pichenettes/shruthi-1/shruthi/hardware_design/documentation/response_notch_lp1.pdf

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

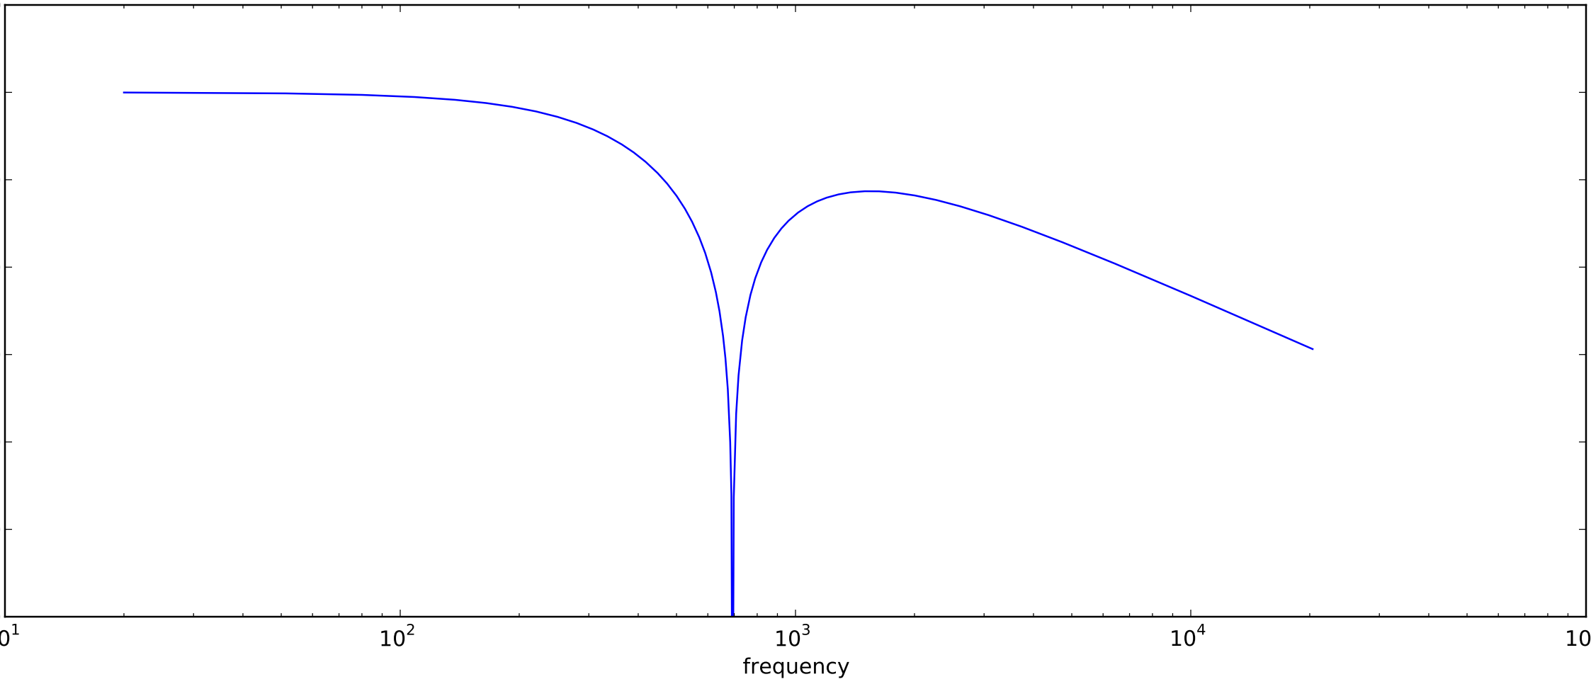
[picture p3: figure]
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
