pichenettes/shruthi-1/shruthi/hardware_design/documentation/response_phaser.pdf

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

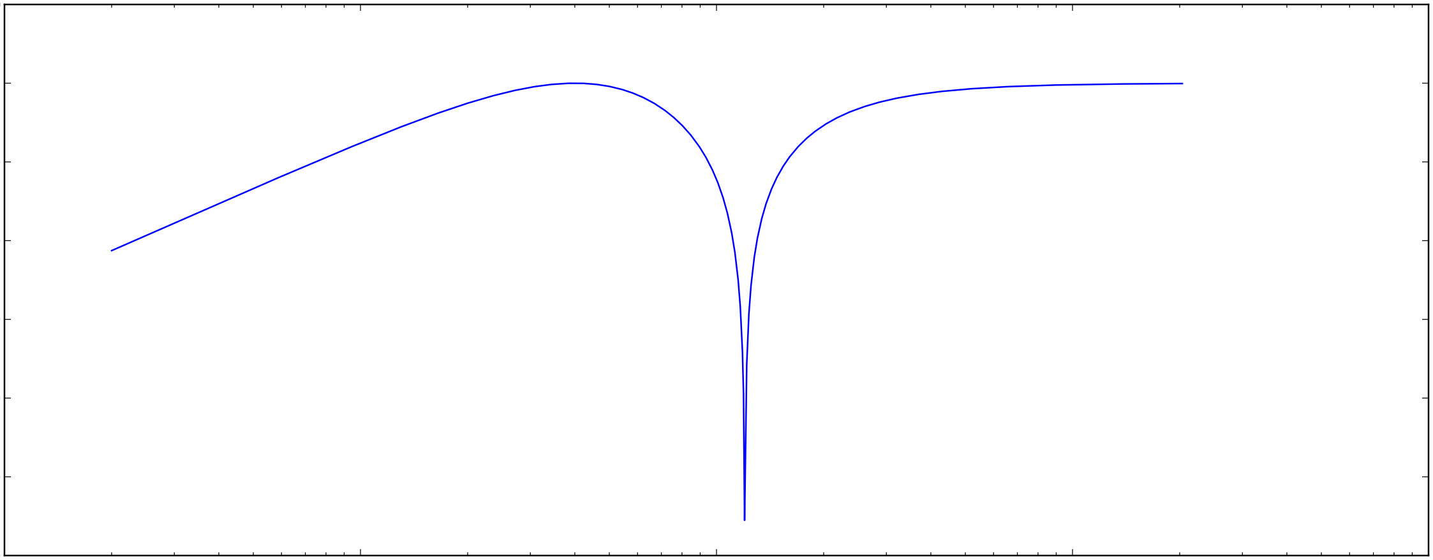
[picture p4: figure]
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
