pichenettes/shruthi-1/shruthi/hardware_design/documentation/smr4mkII_expo_current_source.pdf

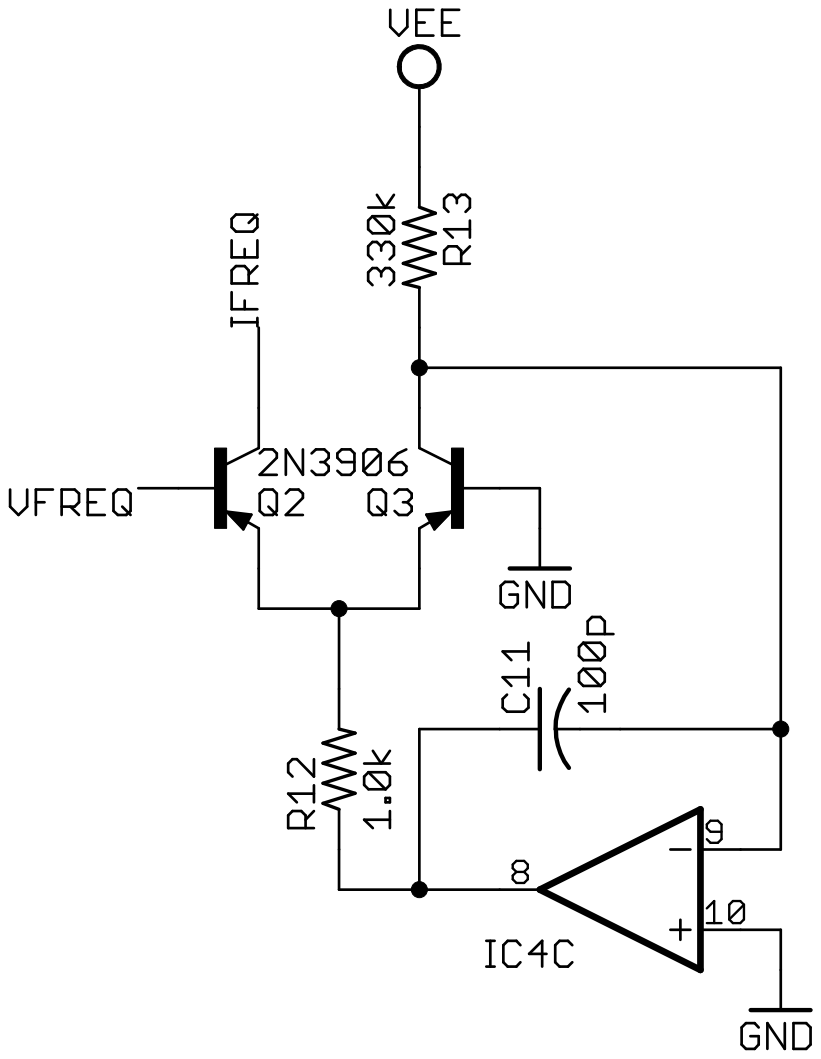
[picture p9: page 1]
