pichenettes/shruthi-1/shruthi/hardware_design/documentation/smr4mkII_linear_current_source.pdf

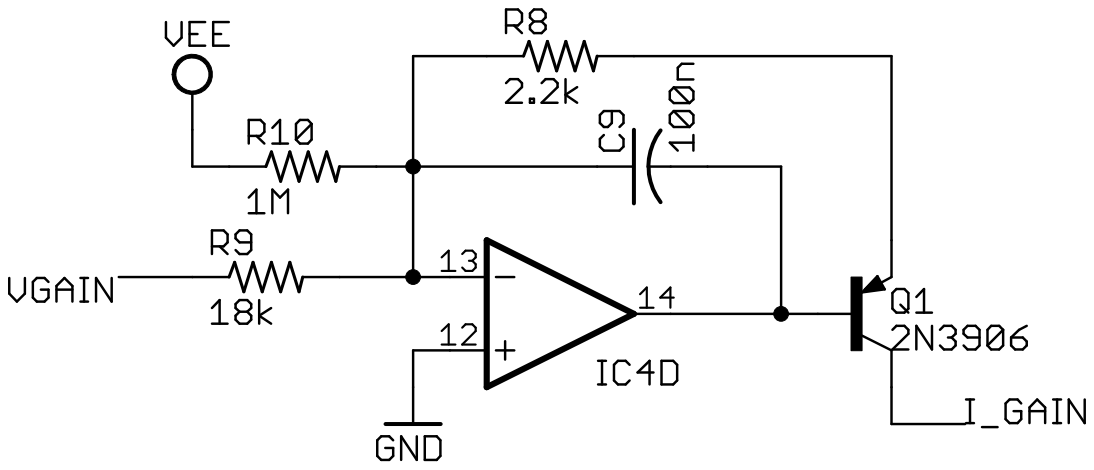
[picture p10: page 1]
