pichenettes/shruthi-1/shruthi/hardware_design/documentation/smr4mkII_otac_cell.pdf

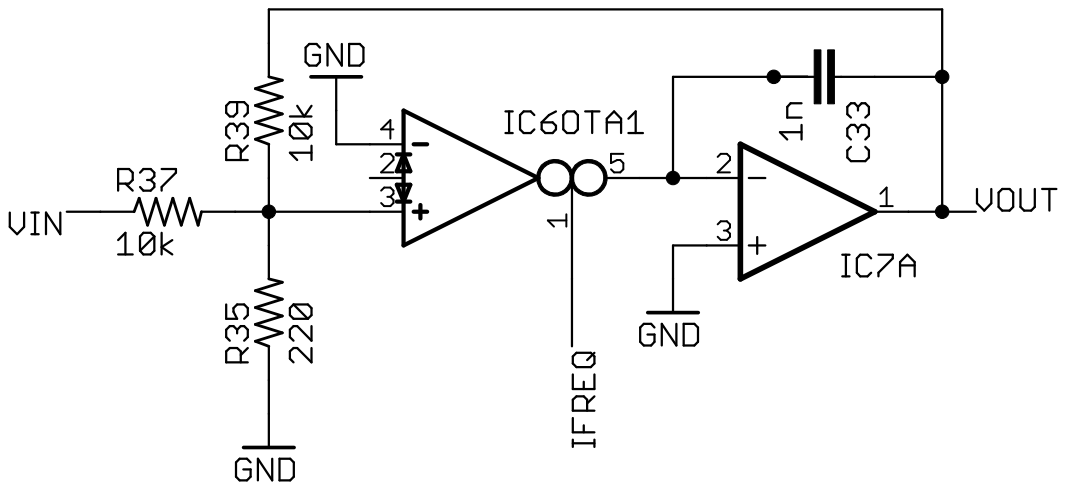
[picture p11: page 1]
