pichenettes/shruthi-1/shruthi/hardware_design/documentation/smr4mkII_scaling.pdf

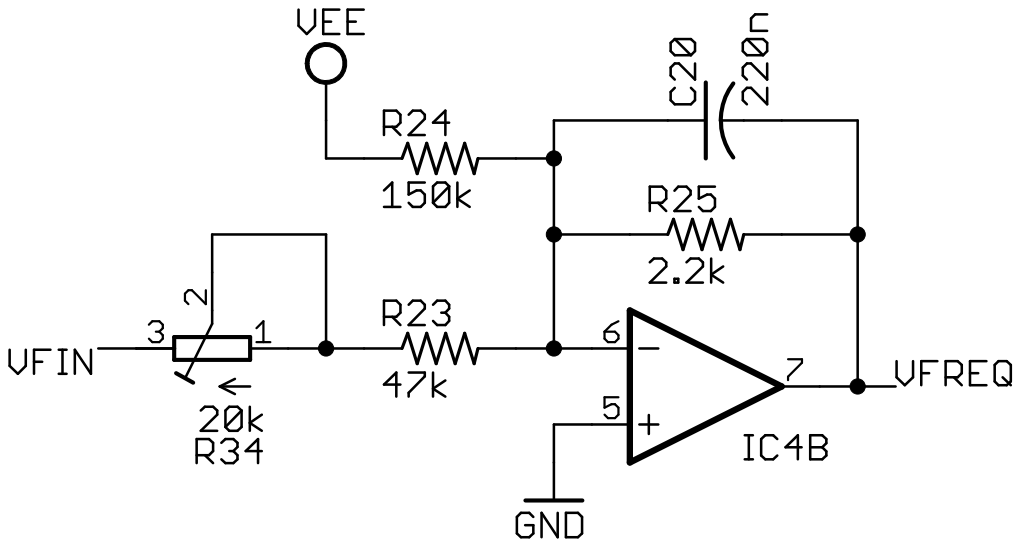
[picture p12: page 1]
