pichenettes/shruthi-1/shruthi/hardware_design/documentation/smr4mkII_vca.pdf

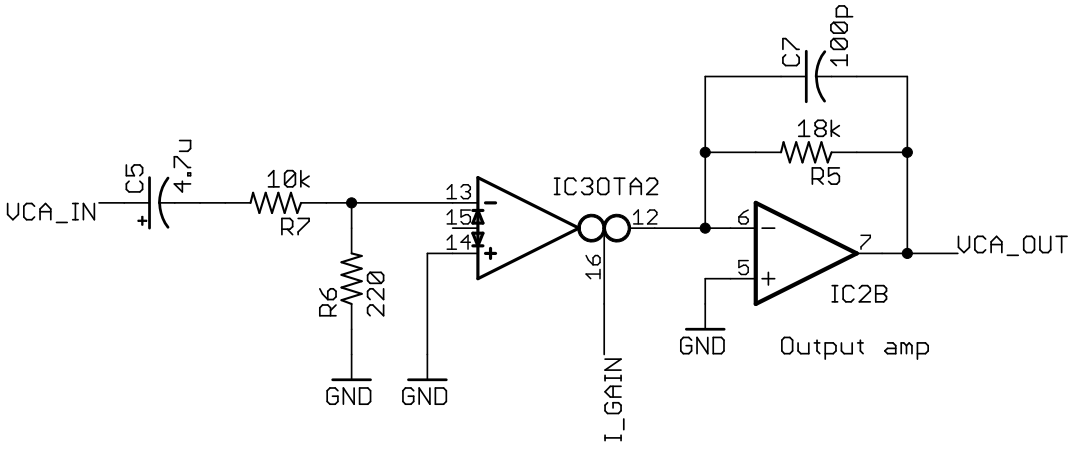
[picture p13: page 1]
