pichenettes/shruthi-1/shruthi/hardware_design/documentation/svf_schematics.pdf

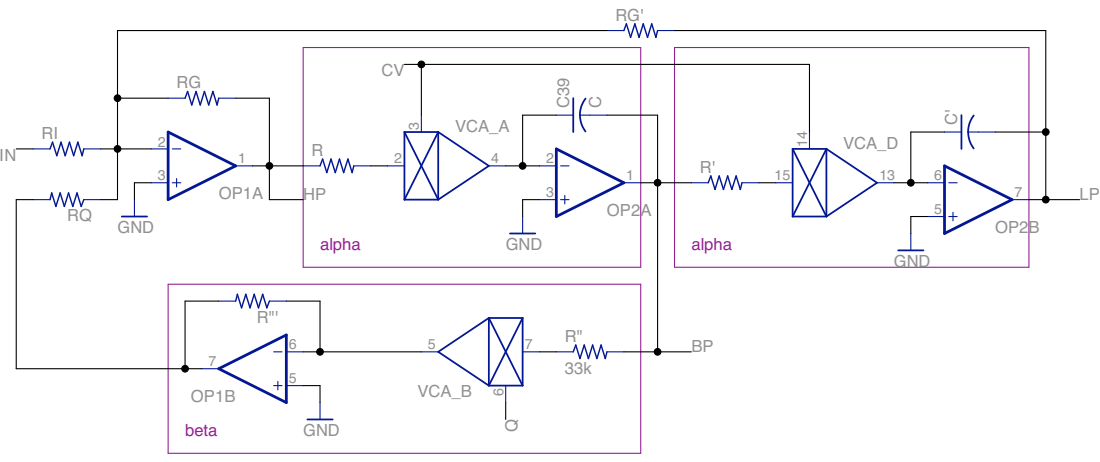
[picture p14: page 1]
