pichenettes/shruthi-1/shruthi/hardware_design/documentation/smr4_otac_cell.pdf

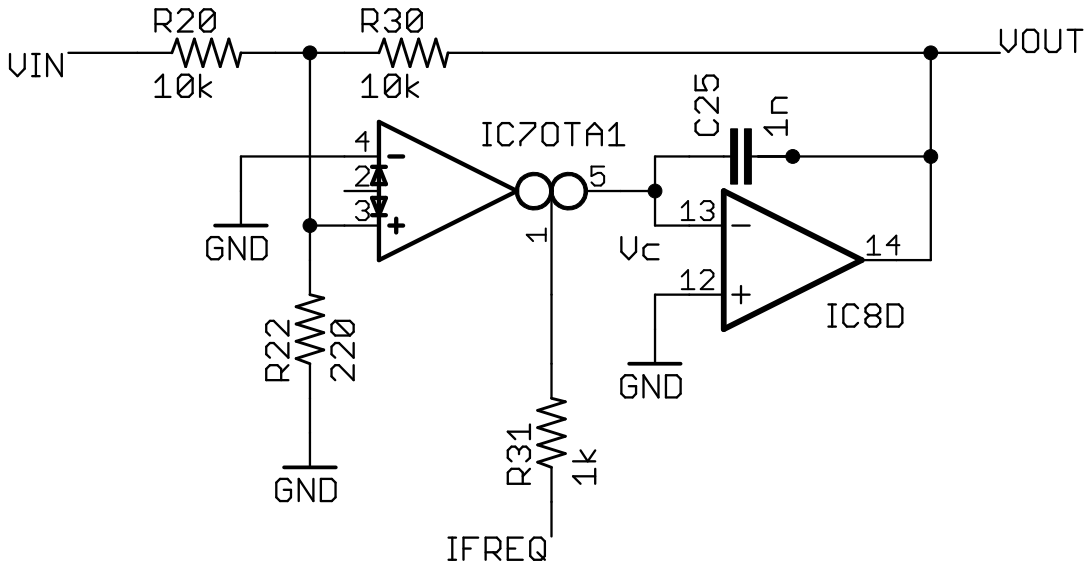
[picture p15: page 1]
