pichenettes/shruthi-1/shruthi/hardware_design/documentation/smr4_expo_current_source.pdf

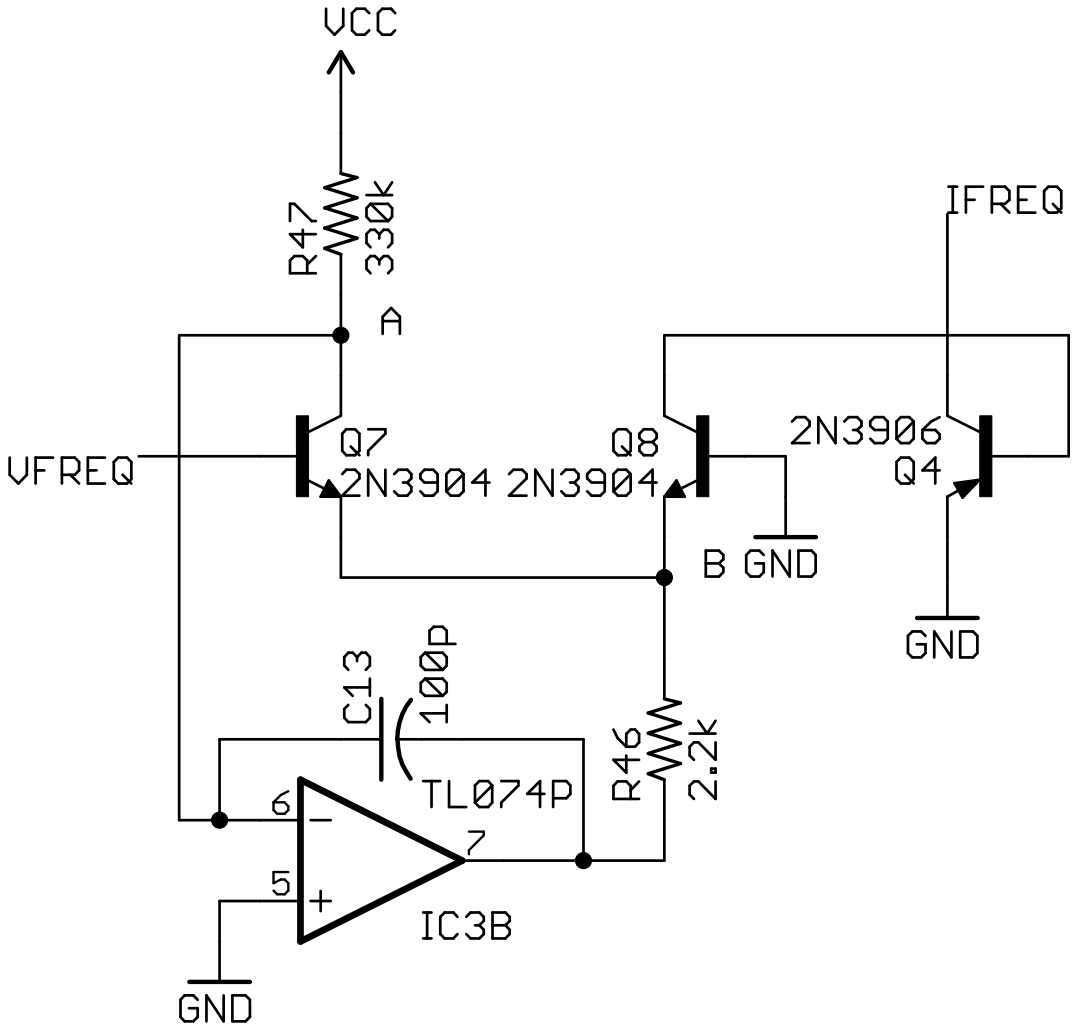
[picture p16: page 1]
