pichenettes/shruthi-1/shruthi/hardware_design/documentation/smr4_scaling.pdf

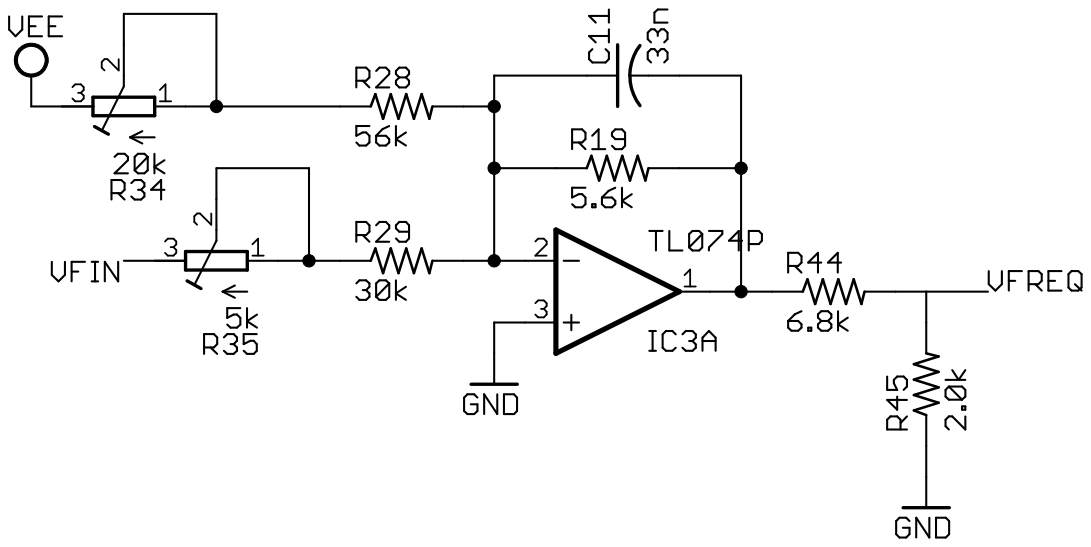
[picture p17: page 1]
