pichenettes/shruthi-1/shruthi/shruthi.h

// Copyright 2009 Emilie Gillet.
//
// Author: Emilie Gillet (emilie.o.gillet@gmail.com)
//
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
// -----------------------------------------------------------------------------
//
// Main definitions.

#ifndef SHRUTHI_SHRUTHI_H_
#define SHRUTHI_SHRUTHI_H_

#include "avrlib/base.h"

#include <avr/pgmspace.h>

namespace shruthi {

enum Switches {
  SWITCH_1,
  SWITCH_2,
  SWITCH_3,
  SWITCH_4,
  SWITCH_MODE,
  SWITCH_LOAD_SAVE,
  SWITCH_SHIFT = SWITCH_LOAD_SAVE,
  SWITCH_ENCODER,
  
  SWITCH_OSC_2_MINUS,
  SWITCH_OSC_2_PLUS,
  SWITCH_OSC_1_MINUS,
  SWITCH_OSC_1_PLUS,
  SWITCH_OP_MINUS,
  SWITCH_OP_PLUS,
  SWITCH_SUB_MINUS,
  SWITCH_SUB_PLUS,

  SWITCH_LFO_1_SHAPE_MINUS,
  SWITCH_LFO_1_SHAPE_PLUS,
  SWITCH_LFO_2_SHAPE_MINUS,
  SWITCH_LFO_2_SHAPE_PLUS,
  SWITCH_PUSH_IT,
  
  SWITCH_LAST,
};

enum Leds {
  LED_1,
  LED_2,
  LED_3,
  LED_4,
  LED_5,
  LED_6,
  LED_MODE,
  LED_WRITE,
  LED_1_MASK = 1 << LED_1,
  LED_2_MASK = 1 << LED_2,
  LED_3_MASK = 1 << LED_3,
  LED_4_MASK = 1 << LED_4,
  LED_5_MASK = 1 << LED_5,
  LED_6_MASK = 1 << LED_6,
  LED_MODE_MASK = 1 << LED_MODE,
  LED_WRITE_MASK = 1 << LED_WRITE,
};

// Set this flag to 6 to get a nice polysynth (humour).
static const uint8_t kNumVoices = 1;
static const uint8_t kPolyphony = 1;

static const uint8_t kNumEditingPots = 4;
static const uint8_t kNumCvInputs = 4;
static const uint8_t kNumLeds = 8;
static const uint8_t kNumSwitches = 6;

// Rate of the main timer. For now, 1 sample is generated per tick, but we might
// want to do something different to achieve other sample rates
// (20kHz or 16kHz).
static const uint16_t kSampleRate = 20000000L / 510;

// One control signal sample is generated for each 40 audio samples (this gives
// the same resolution as for the Shruti-1: 31250/32 ~= 39062/40)
static const uint8_t kControlRate = 40;

// The latency is 1ms, with a buffer storing 4ms of audio.
static const uint8_t kAudioBlockSize = kControlRate;
static const uint8_t kAudioBufferSize = 128;

// ---- LCD display type -------------------------------------------------------

static const uint8_t kLcdWidth = 16;
static const uint8_t kLcdHeight = 2;

// ---- Scheduler configuration ------------------------------------------------

static const uint8_t kSchedulerNumSlots = 32;

// ---- EEPROM size ------------------------------------------------------------

static const uint16_t kBankSize = 8192;
static const uint16_t kMaxNumBanks = 7;  // Tested for 128kb eeprom

}  // namespace shruthi

#endif // SHRUTHI_SHRUTHI_H_
