pichenettes/shruthi-1/burnito/resources.cc

// Copyright 2011 Emilie Gillet.
//
// Author: Emilie Gillet (emilie.o.gillet@gmail.com)
//
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
// -----------------------------------------------------------------------------
//
// Resources definitions.
//
// Automatically generated with:
// make resources


#include "resources.h"

namespace burnito {

const prog_uint8_t blob_res_eeprom_content[] PROGMEM = {
       2,      0,    244,      0,      1,      0,    244,      0,
      10,      0,      7,      0,      0,      0,     36,     23,
      20,     56,     20,     60,      0,     40,     90,    103,
       0,      0,      0,      0,      0,     46,      0,      0,
      21,     16,     31,     22,     16,     63,     19,      2,
       0,      0,      3,      0,      1,      8,      0,      2,
       8,      0,     10,      2,      0,     11,      3,      0,
      20,      1,     63,     21,      0,     38,      8,      6,
      32,      0,      6,     16,    102,    108,     97,    116,
     101,    114,    105,     99,      1,      0,     12,      0,
      13,      0,     14,      0,      0,      0,      0,      0,
       0,      0,      0,     33,      1,     40,      0,      0,
       2,     35,    244,     12,     32,     24,      0,      3,
       3,      4,     26,     40,      0,     81,      0,     54,
       0,     88,     65,     17,      0,     80,      0,      1,
       0,     67,      0,      1,      0,      4,      1,     19,
       5,      0,     19,      3,     22,      0,      3,      0,
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
       0,      0,      3,      0,      0,      0,      4,      0,
      19,      5,      0,     19,      2,      0,      0,      3,
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
};


const prog_uint8_t* blob_table[] = {
  blob_res_eeprom_content,
  blob_res_eeprom_content_tail,
};


}  // namespace burnito
