pichenettes/shruthi-1/dsp/resources.cc

// Copyright 2011 Emilie Gillet.
//
// Author: Emilie Gillet (emilie.o.gillet@gmail.com)
//
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
// -----------------------------------------------------------------------------
//
// Resources definitions.
//
// Automatically generated with:
// make resources


#include "dsp/resources.h"

namespace dsp {

const prog_uint8_t waveform_res_resonance_response[] PROGMEM = {
       0,     27,     36,     43,     48,     53,     57,     60,
      63,     67,     69,     72,     75,     77,     80,     82,
      84,     86,     88,     90,     92,     94,     95,     97,
      99,    100,    102,    104,    105,    107,    108,    110,
     111,    112,    114,    115,    116,    118,    119,    120,
     121,    123,    124,    125,    126,    127,    128,    129,
     131,    132,    133,    134,    135,    136,    137,    138,
     139,    140,    141,    142,    143,    144,    145,    146,
     147,    147,    148,    149,    150,    151,    152,    153,
     154,    154,    155,    156,    157,    158,    159,    159,
     160,    161,    162,    163,    163,    164,    165,    166,
     167,    167,    168,    169,    170,    170,    171,    172,
     172,    173,    174,    175,    175,    176,    177,    177,
     178,    179,    179,    180,    181,    181,    182,    183,
     183,    184,    185,    185,    186,    187,    187,    188,
     189,    189,    190,    190,    191,    192,    192,    193,
     194,    194,    195,    195,    196,    197,    197,    198,
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
  lut_res_phase_increment,
  lut_res_delay_duration,
  lut_res_delay_decimation,
  lut_res_delay_filter_gain,
  lut_res_delay_phase_scaling,
  lut_res_tap_delay_duration,
  lut_res_tap_delay_decimation,
  lut_res_tap_delay_filter_gain,
  lut_res_pitch_ratio,
};


}  // namespace dsp
