pichenettes/shruthi-1/shruthi/resources.cc

// Copyright 2009 Emilie Gillet.
//
// Author: Emilie Gillet (emilie.o.gillet@gmail.com)
//
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
// -----------------------------------------------------------------------------
//
// Resources definitions.
//
// Automatically generated with:
// make resources


#include "shruthi/resources.h"

namespace shruthi {

static const prog_char str_res_shape[] PROGMEM = "shape";
static const prog_char str_res_parameter[] PROGMEM = "parameter";
static const prog_char str_res_resonance[] PROGMEM = "resonance";
static const prog_char str_res_prm[] PROGMEM = "prm";
static const prog_char str_res_range[] PROGMEM = "range";
static const prog_char str_res_rng[] PROGMEM = "rng";
static const prog_char str_res_op_[] PROGMEM = "op.";
static const prog_char str_res_operator[] PROGMEM = "operator";
static const prog_char str_res_detune[] PROGMEM = "detune";
static const prog_char str_res_osc_mix[] PROGMEM = "osc mix";
static const prog_char str_res_sub_osc_[] PROGMEM = "sub osc.";
static const prog_char str_res_env1Tvcf[] PROGMEM = "env1~vcf";
static const prog_char str_res_lfo2Tvcf[] PROGMEM = "lfo2~vcf";
static const prog_char str_res_attack[] PROGMEM = "attack";
static const prog_char str_res_atk[] PROGMEM = "atk";
static const prog_char str_res_decay[] PROGMEM = "decay";
static const prog_char str_res_sustain[] PROGMEM = "sustain";
static const prog_char str_res_release[] PROGMEM = "release";
static const prog_char str_res_rate[] PROGMEM = "rate";
static const prog_char str_res_modulation[] PROGMEM = "modulation";
static const prog_char str_res_operators[] PROGMEM = "operators";
static const prog_char str_res_mod_[] PROGMEM = "mod.";
static const prog_char str_res_source[] PROGMEM = "source";
static const prog_char str_res_src[] PROGMEM = "src";
static const prog_char str_res_dest_[] PROGMEM = "dest.";
static const prog_char str_res_dst[] PROGMEM = "dst";
static const prog_char str_res_amount[] PROGMEM = "amount";
static const prog_char str_res_amt[] PROGMEM = "amt";
static const prog_char str_res_mode[] PROGMEM = "mode";
static const prog_char str_res_overdrive[] PROGMEM = "overdrive";
static const prog_char str_res__fm[] PROGMEM = "fm";
static const prog_char str_res_flavour[] PROGMEM = "flavour";
static const prog_char str_res_time[] PROGMEM = "time";
static const prog_char str_res_level[] PROGMEM = "level";
static const prog_char str_res_fdb[] PROGMEM = "fdb";
static const prog_char str_res_feedback[] PROGMEM = "feedback";
static const prog_char str_res_eq_[] PROGMEM = "eq.";
static const prog_char str_res_fdbck_eq_[] PROGMEM = "fdbck eq.";
static const prog_char str_res_tempo[] PROGMEM = "tempo";
static const prog_char str_res_bpm[] PROGMEM = "bpm";
static const prog_char str_res_groove[] PROGMEM = "groove";
static const prog_char str_res_direction[] PROGMEM = "direction";
static const prog_char str_res_pattern[] PROGMEM = "pattern";
static const prog_char str_res_division[] PROGMEM = "division";
static const prog_char str_res_start[] PROGMEM = "start";
static const prog_char str_res_length[] PROGMEM = "length";
static const prog_char str_res_octave[] PROGMEM = "octave";
static const prog_char str_res_raga[] PROGMEM = "raga";
static const prog_char str_res_porta[] PROGMEM = "porta";
static const prog_char str_res_prt[] PROGMEM = "prt";
static const prog_char str_res_legato[] PROGMEM = "legato";
static const prog_char str_res_tuning[] PROGMEM = "tuning";
static const prog_char str_res_midi_chan[] PROGMEM = "midi chan";
static const prog_char str_res_chn[] PROGMEM = "chn";
static const prog_char str_res_midi_out[] PROGMEM = "midi out";
static const prog_char str_res_pause[] PROGMEM = "pause";
static const prog_char str_res_startpage[] PROGMEM = "startpage";
static const prog_char str_res_snap[] PROGMEM = "snap";
static const prog_char str_res_oscillator_1[] PROGMEM = "oscillator 1";
static const prog_char str_res_oscillator_2[] PROGMEM = "oscillator 2";
static const prog_char str_res_mixer[] PROGMEM = "mixer";
static const prog_char str_res_filter[] PROGMEM = "filter";
static const prog_char str_res_filterS[] PROGMEM = "filter+";
static const prog_char str_res_mode_1[] PROGMEM = "mode 1";
static const prog_char str_res_mode_2[] PROGMEM = "mode 2";
static const prog_char str_res_md1[] PROGMEM = "md1";
static const prog_char str_res_md2[] PROGMEM = "md2";
static const prog_char str_res_envelope_1[] PROGMEM = "envelope 1";
static const prog_char str_res_envelope_2[] PROGMEM = "envelope 2";
static const prog_char str_res_sequencer[] PROGMEM = "sequencer";
static const prog_char str_res_arpeggio[] PROGMEM = "arpeggio";
static const prog_char str_res_ch1[] PROGMEM = "ch1";
static const prog_char str_res_ch2[] PROGMEM = "ch2";
static const prog_char str_res_11[] PROGMEM = "1";
static const prog_char str_res_12[] PROGMEM = "2";
static const prog_char str_res_step_sequencer[] PROGMEM = "step sequencer";
static const prog_char str_res_keyboard[] PROGMEM = "keyboard";
static const prog_char str_res_midi[] PROGMEM = "midi";
static const prog_char str_res_system[] PROGMEM = "system";
static const prog_char str_res_performance[] PROGMEM = "performance";
static const prog_char str_res_param__1[] PROGMEM = "param. 1";
static const prog_char str_res_param__2[] PROGMEM = "param. 2";
static const prog_char str_res_pr1[] PROGMEM = "pr1";
static const prog_char str_res_pr2[] PROGMEM = "pr2";
static const prog_char str_res_fx_[] PROGMEM = "fx.";
static const prog_char str_res_fx_prog_[] PROGMEM = "fx prog.";
static const prog_char str_res_lpf[] PROGMEM = "lpf";
static const prog_char str_res_bpf[] PROGMEM = "bpf";
static const prog_char str_res_hpf[] PROGMEM = "hpf";
static const prog_char str_res_lpl[] PROGMEM = "lp<";
static const prog_char str_res_bpl[] PROGMEM = "bp<";
static const prog_char str_res_hpl[] PROGMEM = "hp<";
static const prog_char str_res_Slp[] PROGMEM = "+lp";
static const prog_char str_res_Sbp[] PROGMEM = "+bp";
static const prog_char str_res_Shp[] PROGMEM = "+hp";
static const prog_char str_res_glp[] PROGMEM = ">lp";
static const prog_char str_res_gbp[] PROGMEM = ">bp";
static const prog_char str_res_ghp[] PROGMEM = ">hp";
static const prog_char str_res_lp4[] PROGMEM = "lp4";
static const prog_char str_res_lp3[] PROGMEM = "lp3";
static const prog_char str_res_lp2[] PROGMEM = "lp2";
static const prog_char str_res_lp1[] PROGMEM = "lp1";
static const prog_char str_res_hp1[] PROGMEM = "hp1";
static const prog_char str_res_hp2[] PROGMEM = "hp2";
static const prog_char str_res_hp3[] PROGMEM = "hp3";
static const prog_char str_res_bp2[] PROGMEM = "bp2";
static const prog_char str_res_bp4[] PROGMEM = "bp4";
static const prog_char str_res_notch[] PROGMEM = "notch";
static const prog_char str_res_phaser[] PROGMEM = "phaser";
static const prog_char str_res_h2lp[] PROGMEM = "h2lp";
static const prog_char str_res_h3lp[] PROGMEM = "h3lp";
static const prog_char str_res_nSlp[] PROGMEM = "n+lp";
static const prog_char str_res_pSlp[] PROGMEM = "p+lp";
static const prog_char str_res_lp[] PROGMEM = "lp";
static const prog_char str_res_bp[] PROGMEM = "bp";
static const prog_char str_res_hp[] PROGMEM = "hp";
static const prog_char str_res_ap[] PROGMEM = "ap";
static const prog_char str_res_liquid[] PROGMEM = "liquid";
static const prog_char str_res_ms[] PROGMEM = "ms";
static const prog_char str_res_wobbly[] PROGMEM = "wobbly";
static const prog_char str_res_whacky[] PROGMEM = "whacky";
static const prog_char str_res_pw1[] PROGMEM = "pw1";
static const prog_char str_res_pw2[] PROGMEM = "pw2";
static const prog_char str_res_51[] PROGMEM = "1";
static const prog_char str_res_52[] PROGMEM = "2";
static const prog_char str_res_5[] PROGMEM = "";
static const prog_char str_res_5f[] PROGMEM = "f";
static const prog_char str_res_mix[] PROGMEM = "mix";
static const prog_char str_res_noi[] PROGMEM = "noi";
static const prog_char str_res_sub[] PROGMEM = "sub";
static const prog_char str_res_cut[] PROGMEM = "cut";
static const prog_char str_res_res[] PROGMEM = "res";
static const prog_char str_res_vca[] PROGMEM = "vca";
static const prog_char str_res_cv1[] PROGMEM = "cv1";
static const prog_char str_res_cv2[] PROGMEM = "cv2";
static const prog_char str_res_tr1[] PROGMEM = "tr1";
static const prog_char str_res_a1[] PROGMEM = "a1";
static const prog_char str_res_d1[] PROGMEM = "d1";
static const prog_char str_res_s1[] PROGMEM = "s1";
static const prog_char str_res_r1[] PROGMEM = "r1";
static const prog_char str_res_tr2[] PROGMEM = "tr2";
static const prog_char str_res_a2[] PROGMEM = "a2";
static const prog_char str_res_d2[] PROGMEM = "d2";
static const prog_char str_res_s2[] PROGMEM = "s2";
static const prog_char str_res_r2[] PROGMEM = "r2";
static const prog_char str_res__lf1[] PROGMEM = "lf1";
static const prog_char str_res__lf2[] PROGMEM = "lf2";
static const prog_char str_res_in1[] PROGMEM = "in1";
static const prog_char str_res_in2[] PROGMEM = "in2";
static const prog_char str_res_out[] PROGMEM = "out";
static const prog_char str_res___off[] PROGMEM = "off";
static const prog_char str_res_add[] PROGMEM = "add";
static const prog_char str_res_prd[] PROGMEM = "prd";
static const prog_char str_res_max[] PROGMEM = "max";
static const prog_char str_res_min[] PROGMEM = "min";
static const prog_char str_res__xor[] PROGMEM = "xor";
static const prog_char str_res_ge[] PROGMEM = ">=";
static const prog_char str_res_le[] PROGMEM = "<=";
static const prog_char str_res_qtz[] PROGMEM = "qtz";
static const prog_char str_res_lag[] PROGMEM = "lag";
static const prog_char str_res_pwm1[] PROGMEM = "pwm1";
static const prog_char str_res_pwm2[] PROGMEM = "pwm2";
static const prog_char str_res_osc1[] PROGMEM = "osc1";
static const prog_char str_res_osc2[] PROGMEM = "osc2";
static const prog_char str_res_osc1S2[] PROGMEM = "osc1+2";
static const prog_char str_res_fine[] PROGMEM = "fine";
static const prog_char str_res_noise[] PROGMEM = "noise";
static const prog_char str_res_subosc[] PROGMEM = "subosc";
static const prog_char str_res_cutoff[] PROGMEM = "cutoff";
static const prog_char str_res_reso[] PROGMEM = "reso";
static const prog_char str_res_cv_1[] PROGMEM = "cv 1";
static const prog_char str_res_cv_2[] PROGMEM = "cv 2";
static const prog_char str_res_trg_e1[] PROGMEM = "trg e1";
static const prog_char str_res_atk__1[] PROGMEM = "atk. 1";
static const prog_char str_res_dec__1[] PROGMEM = "dec. 1";
static const prog_char str_res_sus__1[] PROGMEM = "sus. 1";
static const prog_char str_res_rel__1[] PROGMEM = "rel. 1";
static const prog_char str_res_trg_e2[] PROGMEM = "trg e2";
static const prog_char str_res_atk__2[] PROGMEM = "atk. 2";
static const prog_char str_res_dec__2[] PROGMEM = "dec. 2";
static const prog_char str_res_sus__2[] PROGMEM = "sus. 2";
static const prog_char str_res_rel__2[] PROGMEM = "rel. 2";
static const prog_char str_res_atk1S2[] PROGMEM = "atk1+2";
static const prog_char str_res__lfo_1[] PROGMEM = "lfo 1";
static const prog_char str_res__lfo_2[] PROGMEM = "lfo 2";
static const prog_char str_res_distrt[] PROGMEM = "distrt";
static const prog_char str_res_crushr[] PROGMEM = "crushr";
static const prog_char str_res_Scmbfl[] PROGMEM = "+cmbfl";
static const prog_char str_res_cmbfl[] PROGMEM = "-cmbfl";
static const prog_char str_res_ringmd[] PROGMEM = "ringmd";
static const prog_char str_res_delay[] PROGMEM = "delay";
static const prog_char str_res_fb_dly[] PROGMEM = "fb dly";
static const prog_char str_res_dubdly[] PROGMEM = "dubdly";
static const prog_char str_res__fbdly[] PROGMEM = "!fbdly";
static const prog_char str_res__dbdly[] PROGMEM = "!dbdly";
static const prog_char str_res__16_dl[] PROGMEM = "/16 dl";
static const prog_char str_res__12_dl[] PROGMEM = "/12 dl";
static const prog_char str_res__8_dly[] PROGMEM = "/8 dly";
static const prog_char str_res_3_16dl[] PROGMEM = "3/16dl";
static const prog_char str_res_looper[] PROGMEM = "looper";
static const prog_char str_res_pitch[] PROGMEM = "pitch";
static const prog_char str_res_lgf[] PROGMEM = "l>f";
static const prog_char str_res_hgf[] PROGMEM = "h>f";
static const prog_char str_res_fgl[] PROGMEM = "f>l";
static const prog_char str_res_fgh[] PROGMEM = "f>h";
static const prog_char str_res_gfx[] PROGMEM = ">fx";
static const prog_char str_res_seq[] PROGMEM = "seq";
static const prog_char str_res__sq1[] PROGMEM = "sq1";
static const prog_char str_res__sq2[] PROGMEM = "sq2";
static const prog_char str_res_arp[] PROGMEM = "arp";
static const prog_char str_res_whl[] PROGMEM = "whl";
static const prog_char str_res_aft[] PROGMEM = "aft";
static const prog_char str_res_bnd[] PROGMEM = "bnd";
static const prog_char str_res_ofs[] PROGMEM = "ofs";
static const prog_char str_res_cv3[] PROGMEM = "cv3";
static const prog_char str_res_cv4[] PROGMEM = "cv4";
static const prog_char str_res_cca[] PROGMEM = "ccA";
static const prog_char str_res_ccb[] PROGMEM = "ccB";
static const prog_char str_res_bre[] PROGMEM = "bre";
static const prog_char str_res_ped[] PROGMEM = "ped";
static const prog_char str_res_en1[] PROGMEM = "en1";
static const prog_char str_res_en2[] PROGMEM = "en2";
static const prog_char str_res_vel[] PROGMEM = "vel";
static const prog_char str_res_rnd[] PROGMEM = "rnd";
static const prog_char str_res_not[] PROGMEM = "not";
static const prog_char str_res_gat[] PROGMEM = "gat";
static const prog_char str_res_aud[] PROGMEM = "aud";
static const prog_char str_res_op1[] PROGMEM = "op1";
static const prog_char str_res_op2[] PROGMEM = "op2";
static const prog_char str_res_e4[] PROGMEM = "=4";
static const prog_char str_res_e8[] PROGMEM = "=8";
static const prog_char str_res_e16[] PROGMEM = "=16";
static const prog_char str_res_e32[] PROGMEM = "=32";
static const prog_char str_res_stpseq[] PROGMEM = "stpseq";
static const prog_char str_res_stpsq1[] PROGMEM = "stpsq1";
static const prog_char str_res_stpsq2[] PROGMEM = "stpsq2";
static const prog_char str_res_mwheel[] PROGMEM = "mwheel";
static const prog_char str_res_afttch[] PROGMEM = "afttch";
static const prog_char str_res_bender[] PROGMEM = "bender";
static const prog_char str_res_offset[] PROGMEM = "offset";
static const prog_char str_res_cv_3[] PROGMEM = "cv 3";
static const prog_char str_res_cv_4[] PROGMEM = "cv 4";
static const prog_char str_res_cc_a[] PROGMEM = "cc A";
static const prog_char str_res_cc_b[] PROGMEM = "cc B";
static const prog_char str_res_breath[] PROGMEM = "breath";
static const prog_char str_res_pedal[] PROGMEM = "pedal";
static const prog_char str_res_env_1[] PROGMEM = "env 1";
static const prog_char str_res_env_2[] PROGMEM = "env 2";
static const prog_char str_res_velo[] PROGMEM = "velo";
static const prog_char str_res_random[] PROGMEM = "random";
static const prog_char str_res_note[] PROGMEM = "note";
static const prog_char str_res_gate[] PROGMEM = "gate";
static const prog_char str_res_audio[] PROGMEM = "audio";
static const prog_char str_res_op__1[] PROGMEM = "op. 1";
static const prog_char str_res_op__2[] PROGMEM = "op. 2";
static const prog_char str_res_e_4[] PROGMEM = "= 4";
static const prog_char str_res_e_8[] PROGMEM = "= 8";
static const prog_char str_res_e_16[] PROGMEM = "= 16";
static const prog_char str_res_e_32[] PROGMEM = "= 32";
static const prog_char str_res_patch[] PROGMEM = "patch";
static const prog_char str_res_sequence[] PROGMEM = "sequence";
static const prog_char str_res_save_midi_kbd[] PROGMEM = "save midi/kbd";
static const prog_char str_res_settings_[] PROGMEM = "settings?";
static const prog_char str_res_start_full_midi[] PROGMEM = "start full midi";
static const prog_char str_res_backup_[] PROGMEM = "backup?";
static const prog_char str_res_browse[] PROGMEM = "browse";
static const prog_char str_res_save[] PROGMEM = "save";
static const prog_char str_res_compare[] PROGMEM = "compare";
static const prog_char str_res_[] PROGMEM = "----";
static const prog_char str_res_v[] PROGMEM = "v";
static const prog_char str_res_671____sn__4370[] PROGMEM = "-1    SN #4370";
static const prog_char str_res_v1_03[] PROGMEM = "v1.03";
static const prog_char str_res_shruthi_classic[] PROGMEM = "shruthi classic";
static const prog_char str_res_4_knobs[] PROGMEM = "(4 knobs)";
static const prog_char str_res_shruthi_xt[] PROGMEM = "shruthi xt";
static const prog_char str_res_classic_fcd72[] PROGMEM = "classic (fcd72)";
static const prog_char str_res_full_control[] PROGMEM = "(full control)";
static const prog_char str_res_lets_jam_[] PROGMEM = "let's jam!";
static const prog_char str_res_extern[] PROGMEM = "extern";
static const prog_char str_res_sum[] PROGMEM = "sum";
static const prog_char str_res_sync[] PROGMEM = "sync";
static const prog_char str_res_ring[] PROGMEM = "ring";
static const prog_char str_res_fuzz[] PROGMEM = "fuzz";
static const prog_char str_res_gg4[] PROGMEM = ">>4";
static const prog_char str_res_gg8[] PROGMEM = ">>8";
static const prog_char str_res_fold[] PROGMEM = "fold";
static const prog_char str_res_bits[] PROGMEM = "bits";
static const prog_char str_res_duo[] PROGMEM = "duo";
static const prog_char str_res_2steps[] PROGMEM = "2steps";
static const prog_char str_res_4steps[] PROGMEM = "4steps";
static const prog_char str_res_8steps[] PROGMEM = "8steps";
static const prog_char str_res_seqmix[] PROGMEM = "seqmix";
static const prog_char str_res_stp[] PROGMEM = "stp";
static const prog_char str_res_free[] PROGMEM = "free";
static const prog_char str_res_slave[] PROGMEM = "slave";
static const prog_char str_res_master[] PROGMEM = "master";
static const prog_char str_res_1shot[] PROGMEM = "1shot";
static const prog_char str_res_1_1[] PROGMEM = "1/1";
static const prog_char str_res_1_2[] PROGMEM = "1/2";
static const prog_char str_res_1_3[] PROGMEM = "1/3";
static const prog_char str_res_1_4[] PROGMEM = "1/4";
static const prog_char str_res_1_6[] PROGMEM = "1/6";
static const prog_char str_res_1_8[] PROGMEM = "1/8";
static const prog_char str_res__12[] PROGMEM = "/12";
static const prog_char str_res__16[] PROGMEM = "/16";
static const prog_char str_res__24[] PROGMEM = "/24";
static const prog_char str_res__32[] PROGMEM = "/32";
static const prog_char str_res__48[] PROGMEM = "/48";
static const prog_char str_res__96[] PROGMEM = "/96";
static const prog_char str_res_swing[] PROGMEM = "swing";
static const prog_char str_res_shuffle[] PROGMEM = "shuffle";
static const prog_char str_res_push[] PROGMEM = "push";
static const prog_char str_res_human[] PROGMEM = "human";
static const prog_char str_res_monkey[] PROGMEM = "monkey";
static const prog_char str_res_thru[] PROGMEM = "thru";
static const prog_char str_res_ctrl[] PROGMEM = "ctrl";
static const prog_char str_res_full[] PROGMEM = "full";
static const prog_char str_res_1Tv[] PROGMEM = "1~|";
static const prog_char str_res_2T1[] PROGMEM = "2~1";
static const prog_char str_res_3T2[] PROGMEM = "3~2";
static const prog_char str_res_4T3[] PROGMEM = "4~3";
static const prog_char str_res_5T4[] PROGMEM = "5~4";
static const prog_char str_res_6T5[] PROGMEM = "6~5";
static const prog_char str_res_7T6[] PROGMEM = "7~6";
static const prog_char str_res_8T7[] PROGMEM = "8~7";
static const prog_char str_res_tri[] PROGMEM = "tri";
static const prog_char str_res_sqr[] PROGMEM = "sqr";
static const prog_char str_res_s_h[] PROGMEM = "s&h";
static const prog_char str_res_ramp[] PROGMEM = "ramp";
static const prog_char str_res_step[] PROGMEM = "step";
static const prog_char str_res_3[] PROGMEM = "";
static const prog_char str_res_4[] PROGMEM = "";
static const prog_char str_res_34[] PROGMEM = "";
static const prog_char str_res__[] PROGMEM = "?";
static const prog_char str_res_played[] PROGMEM = "played";
static const prog_char str_res_on[] PROGMEM = "on";
static const prog_char str_res_pl1[] PROGMEM = "pl1";
static const prog_char str_res_pl2[] PROGMEM = "pl2";
static const prog_char str_res_click[] PROGMEM = "click";
static const prog_char str_res_glitch[] PROGMEM = "glitch";
static const prog_char str_res_blow[] PROGMEM = "blow";
static const prog_char str_res_metal[] PROGMEM = "metal";
static const prog_char str_res_pop[] PROGMEM = "pop";
static const prog_char str_res_none[] PROGMEM = "none";
static const prog_char str_res_saw[] PROGMEM = "saw";
static const prog_char str_res_square[] PROGMEM = "square";
static const prog_char str_res_triang[] PROGMEM = "triang";
static const prog_char str_res_zsaw[] PROGMEM = "zsaw";
static const prog_char str_res_zreso[] PROGMEM = "zreso";
static const prog_char str_res_ztri[] PROGMEM = "ztri";
static const prog_char str_res_zpulse[] PROGMEM = "zpulse";
static const prog_char str_res_zsync[] PROGMEM = "zsync";
static const prog_char str_res_pad[] PROGMEM = "pad";
static const prog_char str_res_waves[] PROGMEM = "waves";
static const prog_char str_res_tampur[] PROGMEM = "tampur";
static const prog_char str_res_digitl[] PROGMEM = "digitl";
static const prog_char str_res_metall[] PROGMEM = "metall";
static const prog_char str_res_bowed[] PROGMEM = "bowed";
static const prog_char str_res_slap[] PROGMEM = "slap";
static const prog_char str_res_organ[] PROGMEM = "organ";
static const prog_char str_res_male[] PROGMEM = "male";
static const prog_char str_res_user[] PROGMEM = "user";
static const prog_char str_res_8bits[] PROGMEM = "8bits";
static const prog_char str_res_crush[] PROGMEM = "crush";
static const prog_char str_res_pwm[] PROGMEM = "pwm";
static const prog_char str_res_vowel[] PROGMEM = "vowel";
static const prog_char str_res_belish[] PROGMEM = "belish";
static const prog_char str_res_polatd[] PROGMEM = "polatd";
static const prog_char str_res_cello[] PROGMEM = "cello";
static const prog_char str_res_clpswp[] PROGMEM = "clpswp";
static const prog_char str_res_female[] PROGMEM = "female";
static const prog_char str_res_fmtvoc[] PROGMEM = "fmtvoc";
static const prog_char str_res_frmnt2[] PROGMEM = "frmnt2";
static const prog_char str_res_res3hp[] PROGMEM = "res3hp";
static const prog_char str_res_electp[] PROGMEM = "electp";
static const prog_char str_res_vibes[] PROGMEM = "vibes";
static const prog_char str_res_ssm[] PROGMEM = "ssm";
static const prog_char str_res_svf[] PROGMEM = "svf";
static const prog_char str_res_dsp[] PROGMEM = "dsp";
static const prog_char str_res_pvk[] PROGMEM = "pvk";
static const prog_char str_res_4pm[] PROGMEM = "4pm";
static const prog_char str_res_dly[] PROGMEM = "dly";
static const prog_char str_res_sp[] PROGMEM = "sp";
static const prog_char str_res_splash[] PROGMEM = "splash";
static const prog_char str_res_preset[] PROGMEM = "preset";
static const prog_char str_res_equal[] PROGMEM = "equal";
static const prog_char str_res_just[] PROGMEM = "just";
static const prog_char str_res_pythag[] PROGMEM = "pythag";
static const prog_char str_res_1_4_eb[] PROGMEM = "1/4 eb";
static const prog_char str_res_1_4_e[] PROGMEM = "1/4 e";
static const prog_char str_res_1_4_ea[] PROGMEM = "1/4 ea";
static const prog_char str_res_bhaira[] PROGMEM = "bhaira";
static const prog_char str_res_gunakr[] PROGMEM = "gunakr";
static const prog_char str_res_marwa[] PROGMEM = "marwa";
static const prog_char str_res_shree[] PROGMEM = "shree";
static const prog_char str_res_purvi[] PROGMEM = "purvi";
static const prog_char str_res_bilawa[] PROGMEM = "bilawa";
static const prog_char str_res_yaman[] PROGMEM = "yaman";
static const prog_char str_res_kafi[] PROGMEM = "kafi";
static const prog_char str_res_bhimpa[] PROGMEM = "bhimpa";
static const prog_char str_res_darbar[] PROGMEM = "darbar";
static const prog_char str_res_bagesh[] PROGMEM = "bagesh";
static const prog_char str_res_ragesh[] PROGMEM = "ragesh";
static const prog_char str_res_khamaj[] PROGMEM = "khamaj";
static const prog_char str_res_mimal[] PROGMEM = "mi'mal";
static const prog_char str_res_parame[] PROGMEM = "parame";
static const prog_char str_res_ranges[] PROGMEM = "ranges";
static const prog_char str_res_ganges[] PROGMEM = "ganges";
static const prog_char str_res_kamesh[] PROGMEM = "kamesh";
static const prog_char str_res_palas_[] PROGMEM = "palas";
static const prog_char str_res_natbha[] PROGMEM = "natbha";
static const prog_char str_res_m_kaun[] PROGMEM = "m.kaun";
static const prog_char str_res_bairag[] PROGMEM = "bairag";
static const prog_char str_res_b_todi[] PROGMEM = "b.todi";
static const prog_char str_res_chandr[] PROGMEM = "chandr";
static const prog_char str_res_kaushi[] PROGMEM = "kaushi";
static const prog_char str_res_jogesh[] PROGMEM = "jogesh";
static const prog_char str_res_rasia[] PROGMEM = "rasia";


PROGMEM const prog_char* const string_table[] = {
  str_res_shape,
  str_res_parameter,
  str_res_resonance,
  str_res_prm,
  str_res_range,
  str_res_rng,
  str_res_op_,
  str_res_operator,
  str_res_detune,
  str_res_osc_mix,
  str_res_sub_osc_,
  str_res_env1Tvcf,
  str_res_lfo2Tvcf,
  str_res_attack,
  str_res_atk,
  str_res_decay,
  str_res_sustain,
  str_res_release,
  str_res_rate,
  str_res_modulation,
  str_res_operators,
  str_res_mod_,
  str_res_source,
  str_res_src,
  str_res_dest_,
  str_res_dst,
  str_res_amount,
  str_res_amt,
  str_res_mode,
  str_res_overdrive,
  str_res__fm,
  str_res_flavour,
  str_res_time,
  str_res_level,
  str_res_fdb,
  str_res_feedback,
  str_res_eq_,
  str_res_fdbck_eq_,
  str_res_tempo,
  str_res_bpm,
  str_res_groove,
  str_res_direction,
  str_res_pattern,
  str_res_division,
  str_res_start,
  str_res_length,
  str_res_octave,
  str_res_raga,
  str_res_porta,
  str_res_prt,
  str_res_legato,
  str_res_tuning,
  str_res_midi_chan,
  str_res_chn,
  str_res_midi_out,
  str_res_pause,
  str_res_startpage,
  str_res_snap,
  str_res_oscillator_1,
  str_res_oscillator_2,
  str_res_mixer,
  str_res_filter,
  str_res_filterS,
  str_res_mode_1,
  str_res_mode_2,
  str_res_md1,
  str_res_md2,
  str_res_envelope_1,
  str_res_envelope_2,
  str_res_sequencer,
  str_res_arpeggio,
  str_res_ch1,
  str_res_ch2,
  str_res_11,
  str_res_12,
  str_res_step_sequencer,
  str_res_keyboard,
  str_res_midi,
  str_res_system,
  str_res_performance,
  str_res_param__1,
  str_res_param__2,
  str_res_pr1,
  str_res_pr2,
  str_res_fx_,
  str_res_fx_prog_,
  str_res_lpf,
  str_res_bpf,
  str_res_hpf,
  str_res_lpl,
  str_res_bpl,
  str_res_hpl,
  str_res_Slp,
  str_res_Sbp,
  str_res_Shp,
  str_res_glp,
  str_res_gbp,
  str_res_ghp,
  str_res_lp4,
  str_res_lp3,
  str_res_lp2,
  str_res_lp1,
  str_res_hp1,
  str_res_hp2,
  str_res_hp3,
  str_res_bp2,
  str_res_bp4,
  str_res_notch,
  str_res_phaser,
  str_res_h2lp,
  str_res_h3lp,
  str_res_nSlp,
  str_res_pSlp,
  str_res_lp,
  str_res_bp,
  str_res_hp,
  str_res_ap,
  str_res_liquid,
  str_res_ms,
  str_res_wobbly,
  str_res_whacky,
  str_res_pw1,
  str_res_pw2,
  str_res_51,
  str_res_52,
  str_res_5,
  str_res_5f,
  str_res_mix,
  str_res_noi,
  str_res_sub,
  str_res_cut,
  str_res_res,
  str_res_vca,
  str_res_cv1,
  str_res_cv2,
  str_res_tr1,
  str_res_a1,
  str_res_d1,
  str_res_s1,
  str_res_r1,
  str_res_tr2,
  str_res_a2,
  str_res_d2,
  str_res_s2,
  str_res_r2,
  str_res_atk,
  str_res__lf1,
  str_res__lf2,
  str_res_in1,
  str_res_in2,
  str_res_out,
  str_res___off,
  str_res_add,
  str_res_prd,
  str_res_max,
  str_res_min,
  str_res__xor,
  str_res_ge,
  str_res_le,
  str_res_qtz,
  str_res_lag,
  str_res_pwm1,
  str_res_pwm2,
  str_res_osc1,
  str_res_osc2,
  str_res_osc1S2,
  str_res_fine,
  str_res_mix,
  str_res_noise,
  str_res_subosc,
  str_res_cutoff,
  str_res_reso,
  str_res_vca,
  str_res_cv_1,
  str_res_cv_2,
  str_res_trg_e1,
  str_res_atk__1,
  str_res_dec__1,
  str_res_sus__1,
  str_res_rel__1,
  str_res_trg_e2,
  str_res_atk__2,
  str_res_dec__2,
  str_res_sus__2,
  str_res_rel__2,
  str_res_atk1S2,
  str_res__lfo_1,
  str_res__lfo_2,
  str_res_distrt,
  str_res_crushr,
  str_res_Scmbfl,
  str_res_cmbfl,
  str_res_ringmd,
  str_res_delay,
  str_res_fb_dly,
  str_res_dubdly,
  str_res__fbdly,
  str_res__dbdly,
  str_res__16_dl,
  str_res__12_dl,
  str_res__8_dly,
  str_res_3_16dl,
  str_res_looper,
  str_res_pitch,
  str_res_lgf,
  str_res_hgf,
  str_res_fgl,
  str_res_fgh,
  str_res_gfx,
  str_res__lf1,
  str_res__lf2,
  str_res_seq,
  str_res__sq1,
  str_res__sq2,
  str_res_arp,
  str_res_whl,
  str_res_aft,
  str_res_bnd,
  str_res_ofs,
  str_res_cv1,
  str_res_cv2,
  str_res_cv3,
  str_res_cv4,
  str_res_cca,
  str_res_ccb,
  str_res_bre,
  str_res_ped,
  str_res_noi,
  str_res_en1,
  str_res_en2,
  str_res_vel,
  str_res_rnd,
  str_res_not,
  str_res_gat,
  str_res_aud,
  str_res_op1,
  str_res_op2,
  str_res_e4,
  str_res_e8,
  str_res_e16,
  str_res_e32,
  str_res__lfo_1,
  str_res__lfo_2,
  str_res_stpseq,
  str_res_stpsq1,
  str_res_stpsq2,
  str_res_arp,
  str_res_mwheel,
  str_res_afttch,
  str_res_bender,
  str_res_offset,
  str_res_cv_1,
  str_res_cv_2,
  str_res_cv_3,
  str_res_cv_4,
  str_res_cc_a,
  str_res_cc_b,
  str_res_breath,
  str_res_pedal,
  str_res_noise,
  str_res_env_1,
  str_res_env_2,
  str_res_velo,
  str_res_random,
  str_res_note,
  str_res_gate,
  str_res_audio,
  str_res_op__1,
  str_res_op__2,
  str_res_e_4,
  str_res_e_8,
  str_res_e_16,
  str_res_e_32,
  str_res_patch,
  str_res_sequence,
  str_res_save_midi_kbd,
  str_res_settings_,
  str_res_start_full_midi,
  str_res_backup_,
  str_res_browse,
  str_res_save,
  str_res_compare,
  str_res_,
  str_res_v,
  str_res_671____sn__4370,
  str_res_v1_03,
  str_res_shruthi_classic,
  str_res_4_knobs,
  str_res_shruthi_xt,
  str_res_classic_fcd72,
  str_res_shruthi_xt,
  str_res_full_control,
  str_res_lets_jam_,
  str_res_extern,
  str_res_sum,
  str_res_sync,
  str_res_ring,
  str_res__xor,
  str_res_fuzz,
  str_res_gg4,
  str_res_gg8,
  str_res_fold,
  str_res_bits,
  str_res_duo,
  str_res_2steps,
  str_res_4steps,
  str_res_8steps,
  str_res_seqmix,
  str_res_stp,
  str_res_arp,
  str_res_seq,
  str_res_free,
  str_res_slave,
  str_res_master,
  str_res_1shot,
  str_res_1_1,
  str_res_1_2,
  str_res_1_3,
  str_res_1_4,
  str_res_1_6,
  str_res_1_8,
  str_res__12,
  str_res__16,
  str_res__24,
  str_res__32,
  str_res__48,
  str_res__96,
  str_res_swing,
  str_res_shuffle,
  str_res_push,
  str_res_lag,
  str_res_human,
  str_res_monkey,
  str_res___off,
  str_res_thru,
  str_res_seq,
  str_res_ctrl,
  str_res_full,
  str_res_1Tv,
  str_res_2T1,
  str_res_3T2,
  str_res_4T3,
  str_res_5T4,
  str_res_6T5,
  str_res_7T6,
  str_res_8T7,
  str_res_tri,
  str_res_sqr,
  str_res_s_h,
  str_res_ramp,
  str_res_step,
  str_res_3,
  str_res_4,
  str_res_34,
  str_res__,
  str_res_played,
  str_res___off,
  str_res_on,
  str_res__sq1,
  str_res_tr1,
  str_res_pl1,
  str_res__sq2,
  str_res_tr2,
  str_res_pl2,
  str_res_click,
  str_res_glitch,
  str_res_blow,
  str_res_metal,
  str_res_pop,
  str_res_none,
  str_res_saw,
  str_res_square,
  str_res_triang,
  str_res_zsaw,
  str_res_zreso,
  str_res_ztri,
  str_res_zpulse,
  str_res_zsync,
  str_res_pad,
  str_res__fm,
  str_res_waves,
  str_res_tampur,
  str_res_digitl,
  str_res_metall,
  str_res_bowed,
  str_res_slap,
  str_res_organ,
  str_res_male,
  str_res_user,
  str_res_8bits,
  str_res_crush,
  str_res_pwm,
  str_res_noise,
  str_res_vowel,
  str_res_belish,
  str_res_polatd,
  str_res_cello,
  str_res_clpswp,
  str_res_female,
  str_res_fmtvoc,
  str_res_frmnt2,
  str_res_res3hp,
  str_res_electp,
  str_res_vibes,
  str_res_lpf,
  str_res_ssm,
  str_res_svf,
  str_res_dsp,
  str_res_pvk,
  str_res_4pm,
  str_res_dly,
  str_res_sp,
  str_res_splash,
  str_res_filter,
  str_res_preset,
  str_res_equal,
  str_res_just,
  str_res_pythag,
  str_res_1_4_eb,
  str_res_1_4_e,
  str_res_1_4_ea,
  str_res_bhaira,
  str_res_gunakr,
  str_res_marwa,
  str_res_shree,
  str_res_purvi,
  str_res_bilawa,
  str_res_yaman,
  str_res_kafi,
  str_res_bhimpa,
  str_res_darbar,
  str_res_bagesh,
  str_res_ragesh,
  str_res_khamaj,
  str_res_mimal,
  str_res_parame,
  str_res_ranges,
  str_res_ganges,
  str_res_kamesh,
  str_res_palas_,
  str_res_natbha,
  str_res_m_kaun,
  str_res_bairag,
  str_res_b_todi,
  str_res_chandr,
  str_res_kaushi,
  str_res_jogesh,
  str_res_rasia,
};

const prog_uint16_t lut_res_lfo_increments[] PROGMEM = {
       4,      4,      4,      4,      5,      5,      5,      6,
       6,      7,      7,      7,      8,      8,      9,      9,
      10,     11,     11,     12,     13,     14,     14,     15,
      16,     17,     18,     20,     21,     22,     23,     25,
      26,     28,     30,     31,     33,     35,     37,     40,
      42,     45,     47,     50,     53,     57,     60,     64,
      67,     71,     76,     80,     85,     90,     96,    101,
     108,    114,    121,    128,    136,    144,    153,    162,
     172,    182,    193,    204,    217,    230,    243,    258,
     273,    290,    307,    325,    345,    366,    388,    411,
     435,    461,    489,    518,    549,    582,    617,    654,
     693,    735,    779,    825,    875,    927,    982,   1041,
    1104,   1170,   1240,   1314,   1392,   1476,   1564,   1657,
    1757,   1862,   1973,   2091,   2216,   2349,   2489,   2638,
    2796,   2963,   3141,   3329,   3528,   3739,   3962,   4199,
    4451,   4717,   4999,   5298,   5615,   5951,   6307,   6684,
};
const prog_uint16_t lut_res_env_portamento_increments[] PROGMEM = {
   65535,  18904,  16417,  14306,  12507,  10968,   9647,   8509,
    7525,   6672,   5931,   5285,   4719,   4224,   3788,   3405,
    3066,   2766,   2500,   2264,   2053,   1865,   1697,   1546,
    1411,   1290,   1180,   1082,    993,    912,    839,    773,
     713,    658,    608,    562,    521,    483,    448,    416,
     387,    360,    335,    313,    292,    272,    255,    238,
     223,    209,    196,    184,    172,    162,    152,    143,
     135,    127,    119,    113,    106,    100,     95,     90,
      85,     80,     76,     72,     68,     64,     61,     58,
      55,     52,     50,     47,     45,     43,     41,     39,
      37,     35,     33,     32,     30,     29,     28,     26,
      25,     24,     23,     22,     21,     20,     19,     18,
      18,     17,     16,     16,     15,     14,     14,     13,
      13,     12,     12,     11,     11,     10,     10,      9,
       9,      9,      8,      7,      7,      6,      6,      5,
       5,      4,      4,      3,      3,      2,      2,      1,
};
const prog_uint16_t lut_res_oscillator_increments[] PROGMEM = {
   11104,  11185,  11266,  11347,  11430,  11512,  11596,  11680,
   11765,  11850,  11936,  12022,  12109,  12197,  12285,  12374,
   12464,  12554,  12645,  12737,  12829,  12922,  13016,  13110,
   13205,  13301,  13397,  13494,  13592,  13691,  13790,  13890,
   13991,  14092,  14194,  14297,  14401,  14505,  14610,  14716,
   14822,  14930,  15038,  15147,  15257,  15367,  15479,  15591,
   15704,  15818,  15932,  16048,  16164,  16281,  16399,  16518,
   16638,  16758,  16880,  17002,  17125,  17249,  17374,  17500,
   17627,  17755,  17884,  18013,  18144,  18275,  18408,  18541,
   18675,  18811,  18947,  19084,  19223,  19362,  19502,  19643,
   19786,  19929,  20074,  20219,  20366,  20513,  20662,  20812,
   20962,  21114,  21267,  21421,  21577,  21733,  21890,  22049,
   22209,
};
const prog_uint16_t lut_res_fm_frequency_ratios[] PROGMEM = {
      32,     64,    128,    129,    181,    201,    256,    257,
     362,    402,    448,    512,    514,    576,    704,    724,
     768,    804,    886,   1024,   1086,   1206,   1280,   1448,
    2048,
};
const prog_uint16_t lut_res_scale_just[] PROGMEM = {
       0,     15,      5,     20,    -17,     -2,    -12,      2,
      17,    -20,     -5,    -15,
};
const prog_uint16_t lut_res_scale_pythagorean[] PROGMEM = {
       0,     15,      5,     -7,     10,     -2,    -12,      2,
      17,    -20,     -5,     12,
};
const prog_uint16_t lut_res_scale_1_4_eb[] PROGMEM = {
       0,      0,      0,      0,    -64,      0,      0,      0,
       0,      0,      0,    -64,
};
const prog_uint16_t lut_res_scale_1_4_e[] PROGMEM = {
       0,      0,      0,      0,    -64,      0,      0,      0,
       0,      0,      0,      0,
};
const prog_uint16_t lut_res_scale_1_4_ea[] PROGMEM = {
       0,      0,      0,      0,    -64,      0,      0,      0,
       0,    -64,      0,      0,
};
const prog_uint16_t lut_res_scale_bhairav[] PROGMEM = {
       0,    -12,  32767,  32767,    -17,     -2,  32767,      2,
     -10,  32767,  32767,    -15,
};
const prog_uint16_t lut_res_scale_gunakri[] PROGMEM = {
       0,     15,  32767,  32767,  32767,     -2,  32767,      2,
      17,  32767,  32767,  32767,
};
const prog_uint16_t lut_res_scale_marwa[] PROGMEM = {
       0,     15,  32767,  32767,    -17,  32767,    -12,  32767,
   32767,    -20,  32767,    -15,
};
const prog_uint16_t lut_res_scale_shree[] PROGMEM = {
       0,    -12,  32767,  32767,    -17,  32767,    -12,      2,
     -10,  32767,  32767,    -15,
};
const prog_uint16_t lut_res_scale_purvi[] PROGMEM = {
       0,     15,  32767,  32767,    -17,  32767,    -12,      2,
      17,  32767,  32767,    -15,
};
const prog_uint16_t lut_res_scale_bilawal[] PROGMEM = {
       0,  32767,      5,  32767,    -17,     -2,  32767,      2,
   32767,      7,  32767,    -15,
};
const prog_uint16_t lut_res_scale_yaman[] PROGMEM = {
       0,  32767,      5,  32767,     10,  32767,     15,      2,
   32767,      7,  32767,     12,
};
const prog_uint16_t lut_res_scale_kafi[] PROGMEM = {
       0,  32767,    -22,     -7,  32767,     -2,  32767,      2,
   32767,    -20,     -5,  32767,
};
const prog_uint16_t lut_res_scale_bhimpalasree[] PROGMEM = {
       0,  32767,      5,     20,  32767,     -2,  32767,      2,
   32767,      7,     22,  32767,
};
const prog_uint16_t lut_res_scale_darbari[] PROGMEM = {
       0,  32767,      5,     -7,  32767,     -2,  32767,      2,
     -10,  32767,     -5,  32767,
};
const prog_uint16_t lut_res_scale_rageshree[] PROGMEM = {
       0,  32767,      5,  32767,    -17,     -2,  32767,      2,
   32767,    -20,     -5,  32767,
};
const prog_uint16_t lut_res_scale_khamaj[] PROGMEM = {
       0,  32767,      5,  32767,    -17,     -2,  32767,      2,
   32767,      7,     -5,     12,
};
const prog_uint16_t lut_res_scale_mimal[] PROGMEM = {
       0,  32767,      5,     -7,  32767,     -2,  32767,      2,
   32767,    -20,     -5,    -15,
};
const prog_uint16_t lut_res_scale_parameshwari[] PROGMEM = {
       0,    -12,  32767,     -7,  32767,     -2,  32767,  32767,
   32767,    -20,     -5,  32767,
};
const prog_uint16_t lut_res_scale_rangeshwari[] PROGMEM = {
       0,  32767,      5,     -7,  32767,     -2,  32767,      2,
   32767,  32767,  32767,    -15,
};
const prog_uint16_t lut_res_scale_gangeshwari[] PROGMEM = {
       0,  32767,  32767,  32767,    -17,     -2,  32767,      2,
     -10,  32767,     -5,  32767,
};
const prog_uint16_t lut_res_scale_kameshwari[] PROGMEM = {
       0,  32767,      5,  32767,  32767,  32767,    -12,      2,
   32767,    -20,     -5,  32767,
};
const prog_uint16_t lut_res_scale_palas_kafi[] PROGMEM = {
       0,  32767,      5,     -7,  32767,     -2,  32767,      2,
   32767,      7,     -5,  32767,
};
const prog_uint16_t lut_res_scale_natbhairav[] PROGMEM = {
       0,  32767,      5,  32767,    -17,     -2,  32767,      2,
     -10,  32767,  32767,    -15,
};
const prog_uint16_t lut_res_scale_m_kauns[] PROGMEM = {
       0,  32767,      5,  32767,     10,     -2,  32767,  32767,
     -10,  32767,     -5,  32767,
};
const prog_uint16_t lut_res_scale_bairagi[] PROGMEM = {
       0,    -12,  32767,  32767,  32767,     -2,  32767,      2,
   32767,  32767,     -5,  32767,
};
const prog_uint16_t lut_res_scale_b_todi[] PROGMEM = {
       0,    -12,  32767,     -7,  32767,  32767,  32767,      2,
   32767,  32767,     -5,  32767,
};
const prog_uint16_t lut_res_scale_chandradeep[] PROGMEM = {
       0,  32767,  32767,     -7,  32767,     -2,  32767,      2,
   32767,  32767,     -5,  32767,
};
const prog_uint16_t lut_res_scale_kaushik_todi[] PROGMEM = {
       0,  32767,  32767,     -7,  32767,     -2,    -12,  32767,
     -10,  32767,  32767,  32767,
};
const prog_uint16_t lut_res_scale_jogeshwari[] PROGMEM = {
       0,  32767,  32767,     -7,    -17,     -2,  32767,  32767,
   32767,    -20,     -5,  32767,
};
const prog_uint16_t lut_res_arpeggiator_patterns[] PROGMEM = {
   21845,  30583,  62965,  46517,  28527,   2313,  18761,  21065,
   18725,  56283,  30431,  43281,  54553,  28609,  53505,
};
const prog_uint16_t lut_res_groove_swing[] PROGMEM = {
     127,    127,   -127,   -127,    127,    127,   -127,   -127,
     127,    127,   -127,   -127,    127,    127,   -127,   -127,
};
const prog_uint16_t lut_res_groove_shuffle[] PROGMEM = {
     127,   -127,    127,   -127,    127,   -127,    127,   -127,
     127,   -127,    127,   -127,    127,   -127,    127,   -127,
};
const prog_uint16_t lut_res_groove_push[] PROGMEM = {
     -63,    -63,    127,      0,   -127,      0,      0,     88,
       0,      0,     88,    -50,    -88,      0,     88,      0,
};
const prog_uint16_t lut_res_groove_lag[] PROGMEM = {
      19,     44,     93,     -4,     32,    -53,    -90,   -127,
     117,     32,   -102,    -53,    105,    -53,     93,    -53,
};
const prog_uint16_t lut_res_groove_human[] PROGMEM = {
      88,   -101,    107,    -95,     88,    -88,     50,    -38,
      65,    -88,    101,    -95,    101,   -127,     63,    -31,
};
const prog_uint16_t lut_res_groove_monkey[] PROGMEM = {
      70,    -84,     84,   -112,     84,    -98,    112,    -98,
      54,    -70,    127,    -84,    127,   -112,     84,    -84,
};


PROGMEM const prog_uint16_t* const lookup_table_table[] = {
  lut_res_lfo_increments,
  lut_res_env_portamento_increments,
  lut_res_oscillator_increments,
  lut_res_fm_frequency_ratios,
  lut_res_scale_just,
  lut_res_scale_pythagorean,
  lut_res_scale_1_4_eb,
  lut_res_scale_1_4_e,
  lut_res_scale_1_4_ea,
  lut_res_scale_bhairav,
  lut_res_scale_gunakri,
  lut_res_scale_marwa,
  lut_res_scale_shree,
  lut_res_scale_purvi,
  lut_res_scale_bilawal,
  lut_res_scale_yaman,
  lut_res_scale_kafi,
  lut_res_scale_bhimpalasree,
  lut_res_scale_darbari,
  lut_res_scale_kafi,
  lut_res_scale_rageshree,
  lut_res_scale_khamaj,
  lut_res_scale_mimal,
  lut_res_scale_parameshwari,
  lut_res_scale_rangeshwari,
  lut_res_scale_gangeshwari,
  lut_res_scale_kameshwari,
  lut_res_scale_palas_kafi,
  lut_res_scale_natbhairav,
  lut_res_scale_m_kauns,
  lut_res_scale_bairagi,
  lut_res_scale_b_todi,
  lut_res_scale_chandradeep,
  lut_res_scale_kaushik_todi,
  lut_res_scale_jogeshwari,
  lut_res_scale_yaman,
  lut_res_arpeggiator_patterns,
  lut_res_groove_swing,
  lut_res_groove_shuffle,
  lut_res_groove_push,
  lut_res_groove_lag,
  lut_res_groove_human,
  lut_res_groove_monkey,
};

const prog_uint32_t lut_res_tempo_phase_increment[] PROGMEM = {
  35046933, 35923106, 36799279, 37675453, 38551626, 39427799, 40303973, 41180146,
  42056319, 42932493, 43808666, 44684839, 45561013, 46437186, 47313359, 48189533,
  49065706, 49941879, 50818053, 51694226, 52570399, 53446573, 54322746, 55198919,
  56075093, 56951266, 57827439, 58703613, 59579786, 60455959, 61332132, 62208306,
  63084479, 63960652, 64836826, 65712999, 66589172, 67465346, 68341519, 69217692,
  70093866, 70970039, 71846212, 72722386, 73598559, 74474732, 75350906, 76227079,
  77103252, 77979426, 78855599, 79731772, 80607946, 81484119, 82360292, 83236466,
  84112639, 84988812, 85864986, 86741159, 87617332, 88493506, 89369679, 90245852,
  91122026, 91998199, 92874372, 93750546, 94626719, 95502892, 96379066, 97255239,
  98131412, 99007586, 99883759, 100759932, 101636106, 102512279, 103388452, 104264626,
  105140799, 106016972, 106893146, 107769319, 108645492, 109521666, 110397839, 111274012,
  112150186, 113026359, 113902532, 114778706, 115654879, 116531052, 117407226, 118283399,
  119159572, 120035745, 120911919, 121788092, 122664265, 123540439, 124416612, 125292785,
  126168959, 127045132, 127921305, 128797479, 129673652, 130549825, 131425999, 132302172,
  133178345, 134054519, 134930692, 135806865, 136683039, 137559212, 138435385, 139311559,
  140187732, 141063905, 141940079, 142816252, 143692425, 144568599, 145444772, 146320945,
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
      42,     43,     44,     44,     44,     45,     46,     46,
       8,     47,     48,     49,     49,     50,     51,     52,
      53,     53,      0,      0,      0,      0,      0,      0,
       0,      0,      8,     54,     55,     56,     56,     57,
      57,     57,     57,     57,      0,      0,      0,      0,
       0,      0,      0,      0,     16,      3,     58,     58,
     120,     59,     59,     60,     61,     62,     63,     64,
      65,     65,     66,     67,     68,     68,     16,     75,
      69,     70,     71,     72,     73,     74,     75,     76,
      81,     77,     78,     80,     79,     80,     81,     81,
       4,     82,     82,     82,     83,     82,      0,      0,
       0,      0,      0,      0,      0,      0,      0,      0,
       0,      0,      8,     87,     84,     87,    116,     85,
      86,     86,     87,     87,      0,      0,      0,      0,
       0,      0,      0,      0,      4,     88,     89,     90,
      91,     89,      0,      0,      0,      0,      0,      0,
       0,      0,      0,      0,      0,      0,      4,     92,
      92,     93,     94,     82,      0,      0,      0,      0,
       0,      0,      0,      0,      0,      0,      0,      0,
      16,     95,     96,     97,     98,     99,    100,    101,
     102,    103,    104,    105,    106,    107,    108,    109,
     110,    110,      4,    111,    112,    113,    112,    112,
       0,      0,      0,      0,      0,      0,      0,      0,
       0,      0,      0,      0,     16,    120,    120,    114,
     114,    115,    115,    115,    115,    115,    115,    115,
     115,    115,    115,    115,    115,    115,      4,     93,
     116,    117,    118,    119,      0,      0,      0,      0,
       0,      0,      0,      0,      0,      0,      0,      0,
       8,    120,    120,    120,    120,    120,    120,    116,
     121,    121,      0,      0,      0,      0,      0,      0,
       0,      0,      8,    122,    123,    123,    124,    125,
     126,    126,    126,      3,      0,      0,      0,      0,
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
};
const prog_uint8_t wav_res_version[] PROGMEM = {
       1,      0,
};


const prog_uint8_t* const waveform_table[] = {
  wav_res_formant_sine,
  wav_res_formant_square,
  wav_res_sine,
  wav_res_bandlimited_square_0,
  wav_res_bandlimited_square_1,
  wav_res_bandlimited_square_2,
  wav_res_bandlimited_square_3,
  wav_res_bandlimited_square_4,
  wav_res_bandlimited_square_5,
  wav_res_sine,
  wav_res_bandlimited_saw_0,
  wav_res_bandlimited_saw_1,
  wav_res_bandlimited_saw_2,
  wav_res_bandlimited_saw_3,
  wav_res_bandlimited_saw_4,
  wav_res_bandlimited_saw_5,
  wav_res_sine,
  wav_res_bandlimited_triangle_0,
  wav_res_bandlimited_triangle_0,
  wav_res_bandlimited_triangle_0,
  wav_res_bandlimited_triangle_3,
  wav_res_bandlimited_triangle_4,
  wav_res_bandlimited_triangle_5,
  wav_res_sine,
  wav_res_vowel_data,
  wav_res_distortion,
  wav_res_env_expo,
  wav_res_ssm2164_linearization,
  wav_res_waves,
  wav_res_wavetables,
  wav_res_version,
};

const prog_uint8_t chr_res_special_characters[] PROGMEM = {
       2,      3,      3,      2,      2,     14,     30,     12,
       0,      0,      0,      4,      4,     14,     17,     31,
       4,     14,     21,      4,      4,      4,      4,      0,
       0,      4,      4,      4,      4,     21,     14,      4,
       0,      0,      0,      8,     21,      2,      0,      0,
       8,     20,      9,     21,      3,      5,     17,     14,
      14,     17,     27,     29,     21,     23,     17,      0,
};


const prog_uint8_t* const character_table[] = {
  chr_res_special_characters,
};


}  // namespace shruthi
