pichenettes/shruthi-1/shruthi/storage.h

// Copyright 2009 Emilie Gillet.
//
// Author: Emilie Gillet (emilie.o.gillet@gmail.com)
//
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
// -----------------------------------------------------------------------------
//
// Storage for patches, sequences and system settings.

#ifndef SHRUTHI_STORAGE_H_
#define SHRUTHI_STORAGE_H_

#include <avr/eeprom.h>
#include <string.h>

#include "avrlib/base.h"
#include "avrlib/devices/external_eeprom.h"
#include "shruthi/display.h"
#include "shruthi/patch.h"
#include "shruthi/sequencer_settings.h"
#include "shruthi/shruthi.h"
#include "shruthi/system_settings.h"

namespace shruthi {

enum SysExReceptionState {
  RECEIVING_HEADER = 0,
  RECEIVING_OLD_HEADER = 1,
  RECEIVING_COMMAND = 2,
  RECEIVING_DATA = 3,
  RECEIVING_FOOTER = 4,
  RECEPTION_OK = 5,
  RECEPTION_ERROR = 6,
};

template<typename T>
class StorageConfiguration { };

template<> class StorageConfiguration<Patch> {
 public:
  enum {
    num_internal = 16,
    num_external = 64,
    offset_internal = 16,
    offset_external = 0,
    size = PATCH_SIZE,
    sysex_object_id = 0x01,
    undo_buffer_offset = 0,
  };
};

template<> class StorageConfiguration<SequencerSettings> {
 public:
  enum {
    num_internal = 16,
    num_external = 64,
    offset_internal = StorageConfiguration<Patch>::offset_internal + \
        StorageConfiguration<Patch>::num_internal * PATCH_SIZE,
    offset_external = StorageConfiguration<Patch>::offset_external + \
        StorageConfiguration<Patch>::num_external * PATCH_SIZE,
    size = sizeof(SequenceStep) * kNumSteps,
    sysex_object_id = 0x02,
    undo_buffer_offset = PATCH_SIZE,
  };
};

class Storage {
 public:
  static void Init();

  static inline uint8_t sysex_rx_state() {
    return sysex_rx_state_;
  }

  template<typename T>
  static uint16_t size() {
    return StorageConfiguration<T>::num_internal +
           StorageConfiguration<T>::num_external * num_accessible_banks_;
  }

  static uint16_t addressable_space_size() {
    return kInternalEepromSize + num_accessible_banks_ * kBankSize;
  }

  static uint8_t num_accessible_banks() {
    return num_accessible_banks_;
  }

  template<typename T>
  static void SysExDump(T* ptr) {
    ptr->PrepareForWrite();
    SysExDumpBuffer(
        ptr->saved_data(),
        StorageConfiguration<T>::sysex_object_id,
        0,
        StorageConfiguration<T>::size);
  }

  static void SysExBulkDump();

  static void SysExReceive(uint8_t sysex_rx_byte);

  template<typename T>
  static void Backup(T* ptr) {
    ptr->PrepareForWrite();
    memcpy(
        undo_buffer_ + StorageConfiguration<T>::undo_buffer_offset,
        ptr->saved_data(),
        StorageConfiguration<T>::size);
  }
  template<typename T>
  static void Restore(T* ptr) {
    AcceptData(ptr, undo_buffer_ + StorageConfiguration<T>::undo_buffer_offset);
  }

  static void WritePatch(uint16_t slot);
  static void WriteSequence(uint16_t slot);
  static void LoadPatch(uint16_t slot);
  static void LoadSequence(uint16_t slot);
  static void LoadPatchName(uint8_t* destination, uint16_t slot) {
    LoadBytes<Patch>(destination, 68, 8, slot);
  }

  template<typename T>
  static uint8_t AcceptData(T* ptr, uint8_t* data) {
    uint8_t success = ptr->CheckBuffer(data);
    if (success) {
      memcpy(ptr->saved_data(), data, StorageConfiguration<T>::size);
      ptr->Update();
    }
    return success;
  }

 private:
  template<typename T>
  static void Write(T* ptr, uint16_t slot) {
    ptr->PrepareForWrite();
    if (slot < StorageConfiguration<T>::num_internal) {
      eeprom_write_block(
          (uint8_t *)(ptr->saved_data()),
          address<T>(slot),
          StorageConfiguration<T>::size);

    } else {
      WriteExternal(
          (uint8_t *)(ptr->saved_data()),
          (uint16_t)(address<T>(slot)),
          StorageConfiguration<T>::size);
    }
  }
  template<typename T>
  static void Load(T* ptr, uint16_t slot) {
    if (slot < StorageConfiguration<T>::num_internal) {
      eeprom_read_block(
          load_buffer_,
          address<T>(slot),
          StorageConfiguration<T>::size);
    } else {
      ReadExternal(
          load_buffer_,
          (uint16_t)(address<T>(slot)),
          StorageConfiguration<T>::size);
    }
    AcceptData(ptr, load_buffer_);
  }

  template<typename T>
  static void LoadBytes(
      uint8_t* destination,
      uint16_t offset,
      uint16_t size,
      uint16_t slot) {
    if (slot < StorageConfiguration<T>::num_internal) {
      eeprom_read_block(destination, address<T>(slot) + offset, size);
    } else {
      ReadExternal(destination, (uint16_t)(address<T>(slot)) + offset, size);
    }
  }

  template<typename T>
  static uint8_t* address(uint16_t slot) {
    if (slot < StorageConfiguration<T>::num_internal) {
      return (uint8_t*)(
          StorageConfiguration<T>::offset_internal + \
          StorageConfiguration<T>::size * slot);
    } else {
      slot -= StorageConfiguration<T>::num_internal;
      uint16_t base = StorageConfiguration<T>::offset_external;
      while (slot >= StorageConfiguration<T>::num_external) {
        slot -= StorageConfiguration<T>::num_external;
        base += kBankSize;
      }
      return (uint8_t*)(base + StorageConfiguration<T>::size * slot);
    }
  }

  static void WriteExternal(const uint8_t* data, uint16_t address, uint8_t size);
  static void ReadExternal(uint8_t* data, uint16_t address, uint8_t size);
  static void SysExParseCommand();
  static void SysExAcceptBuffer();
  static void SysExDumpBuffer(
      uint8_t* data,
      uint8_t command,
      uint8_t argument,
      uint8_t size);
  static uint8_t undo_buffer_[128];
  static uint8_t load_buffer_[sizeof(Patch)];
  static uint8_t sysex_rx_buffer_[129];
  static uint8_t* sysex_rx_destination_;
  static uint16_t sysex_rx_bytes_received_;
  static uint16_t sysex_rx_expected_size_;
  static uint8_t sysex_rx_state_;
  static uint8_t sysex_rx_checksum_;
  static uint8_t sysex_rx_command_[2];
  static uint8_t num_accessible_banks_;
};

extern avrlib::ExternalEeprom<kBankSize * kMaxNumBanks> external_eeprom;

extern Lcd lcd;


}  // namespace shruthi

#endif // SHRUTHI_PATCH_H_
