pichenettes/shruthi-1/shruthi/note_stack.h

// Copyright 2009 Emilie Gillet.
//
// Author: Emilie Gillet (emilie.o.gillet@gmail.com)
//
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
// -----------------------------------------------------------------------------
//
// Stack of currently pressed keys.
//
// Currently pressed keys are stored as a linked list. The linked list is used
// as a LIFO stack to allow monosynth-like behaviour. An example of such
// behaviour is:
// player presses and holds C4-> C4 is played.
// player presses and holds C5 (while holding C4) -> C5 is played.
// player presses and holds G4 (while holding C4&C5)-> G4 is played.
// player releases C5 -> G4 is played.
// player releases G4 -> C4 is played.
//
// The nodes used in the linked list are pre-allocated from a pool of 16
// nodes, so the "pointers" (to the root element for example) are not actual
// pointers, but indices of an element in the pool.
//
// Additionally, an array of pointers is stored to allow random access to the
// n-th note, sorted by ascending order of pitch (for arpeggiation).
//
// TODO(pichenettes): having this class implemented as a "static singleton"
// saves almost 300 bytes of code. w00t! But we'd rather move this back to a
// simple class when adding multitimbrality. When will we add multitimbrality?
// Probably never.

#ifndef SHRUTHI_NOTE_STACK_H_
#define SHRUTHI_NOTE_STACK_H_

#include "avrlib/base.h"

static const uint8_t kNoteStackSize = 8;

namespace shruthi {

struct NoteEntry {
  uint8_t note;
  uint8_t velocity;
  uint8_t next_ptr;  // Base 1.
};

class NoteStack {
 public: 
  NoteStack() { }
  void Init() { Clear(); }

  void NoteOn(uint8_t note, uint8_t velocity);
  void NoteOff(uint8_t note);
  void Clear();

  uint8_t size() { return size_; }
  uint8_t max_size() { return kNoteStackSize; }
  const NoteEntry& most_recent_note() { return pool_[root_ptr_]; }
  const NoteEntry& least_recent_note() {
    uint8_t current = root_ptr_;
    while (current && pool_[current].next_ptr) {
      current = pool_[current].next_ptr;
    }
    return pool_[current];
  }
  const NoteEntry& sorted_note(uint8_t index) {
    return pool_[sorted_ptr_[index]];
  }
  const NoteEntry& played_note(uint8_t index) const {
    uint8_t current = root_ptr_;
    index = size_ - index - 1;
    for (uint8_t i = 0; i < index; ++i) {
      current = pool_[current].next_ptr;
    }
    return pool_[current];
  }
  const NoteEntry& note(uint8_t index) { return pool_[index]; }
  NoteEntry* mutable_note(uint8_t index) { return &pool_[index]; }
  const NoteEntry& dummy() { return pool_[0]; }

 private:
  uint8_t size_;
  NoteEntry pool_[kNoteStackSize + 1];  // First element is a dummy node!
  uint8_t root_ptr_;  // Base 1.
  uint8_t sorted_ptr_[kNoteStackSize + 1];  // Base 1.

  DISALLOW_COPY_AND_ASSIGN(NoteStack);
};

}  // namespace shruthi

#endif // SHRUTHI_NOTE_STACK_H_
